JJ2PNX/FlukeNIC/firmware/main/mount.c

// Derived from esp-idf sample code
/*
 * SPDX-FileCopyrightText: 2022 Espressif Systems (Shanghai) CO LTD
 *
 * SPDX-License-Identifier: Unlicense OR CC0-1.0
 */
/* HTTP File Server Example, SD card / SPIFFS mount functions.

   This example code is in the Public Domain (or CC0 licensed, at your option.)

   Unless required by applicable law or agreed to in writing, this
   software is distributed on an "AS IS" BASIS, WITHOUT WARRANTIES OR
   CONDITIONS OF ANY KIND, either express or implied.
*/

#include <stdio.h>
#include <string.h>
#include "esp_log.h"
#include "esp_err.h"
#include "esp_vfs_fat.h"
#include "esp_spiffs.h"
#include "sdkconfig.h"
#include "soc/soc_caps.h"
#include "driver/sdspi_host.h"
#include "driver/spi_common.h"
#if SOC_SDMMC_HOST_SUPPORTED
#include "driver/sdmmc_host.h"
#endif
#include "sdmmc_cmd.h"

static const char *TAG = "mount";

#define PIN_NUM_MISO  19
#define PIN_NUM_MOSI  23
#define PIN_NUM_CLK   18
#define PIN_NUM_CS    5
#define PIN_NUM_CD    33

esp_err_t mount_sdcard(const char* base_path)
{
    ESP_LOGI(TAG, "Initializing SD card");

    esp_vfs_fat_sdmmc_mount_config_t mount_config = {
        .format_if_mount_failed = false,
        .max_files = 5,
        .allocation_unit_size = 16 * 1024
    };
    esp_err_t ret;
    sdmmc_card_t* card;

    sdmmc_host_t host = SDSPI_HOST_DEFAULT();
    spi_bus_config_t bus_cfg = {
        .mosi_io_num = PIN_NUM_MOSI,
        .miso_io_num = PIN_NUM_MISO,
        .sclk_io_num = PIN_NUM_CLK,
        .quadwp_io_num = -1,
        .quadhd_io_num = -1,
        .max_transfer_sz = 4000,
    };

    ret = spi_bus_initialize(host.slot, &bus_cfg, SDSPI_DEFAULT_DMA);
    if (ret != ESP_OK) {
        ESP_LOGE(TAG, "Failed to initialize spi bus.");
        return ret;
    }

    // This initializes the slot without card detect (CD) and write protect (WP) signals.
    // Modify slot_config.gpio_cd and slot_config.gpio_wp if your board has these signals.
    sdspi_device_config_t slot_config = SDSPI_DEVICE_CONFIG_DEFAULT();
    slot_config.gpio_cs = PIN_NUM_CS;
    slot_config.gpio_cd = PIN_NUM_CD;
    slot_config.host_id = host.slot;
    ret = esp_vfs_fat_sdspi_mount(base_path, &host, &slot_config, &mount_config, &card);
    if (ret != ESP_OK){
        if (ret == ESP_FAIL) {
            ESP_LOGE(TAG, "Failed to mount filesystem. "
                "If you want the card to be formatted, set the EXAMPLE_FORMAT_IF_MOUNT_FAILED menuconfig option.");
        } else {
            ESP_LOGE(TAG, "Failed to initialize the card (%s). "
                "Make sure SD card lines have pull-up resistors in place.", esp_err_to_name(ret));
        }
        return ret;
    }

    sdmmc_card_print_info(stdout, card);
    return ESP_OK;
}

esp_err_t mount_spiffs(const char* base_path)
{
    ESP_LOGI(TAG, "Initializing SPIFFS");

    esp_vfs_spiffs_conf_t conf = {
        .base_path = base_path,
        .partition_label = NULL,
        .max_files = 5,
        .format_if_mount_failed = false
    };

    esp_err_t ret = esp_vfs_spiffs_register(&conf);
    if (ret != ESP_OK) {
        if (ret == ESP_FAIL) {
            ESP_LOGE(TAG, "Failed to mount or format filesystem");
        } else if (ret == ESP_ERR_NOT_FOUND) {
            ESP_LOGE(TAG, "Failed to find SPIFFS partition");
        } else {
            ESP_LOGE(TAG, "Failed to initialize SPIFFS (%s)", esp_err_to_name(ret));
        }
        return ret;
    }

    size_t total = 0, used = 0;
    ret = esp_spiffs_info(NULL, &total, &used);
    if (ret != ESP_OK) {
        ESP_LOGE(TAG, "Failed to get SPIFFS partition information (%s)", esp_err_to_name(ret));
        return ret;
    }

    ESP_LOGI(TAG, "Partition size: total: %d, used: %d", total, used);
    return ESP_OK;
}
